dusanstojkovic/pengy/firmware/docs/CubeCell HTCC-AB01 - back.png

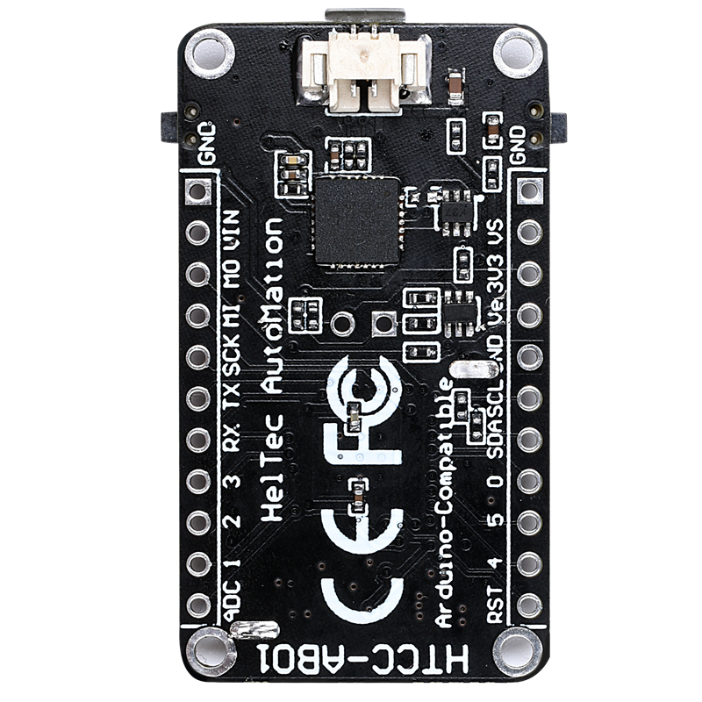
firmware/docs/CubeCell HTCC-AB01 - back.png
