dusanstojkovic/pengy/media/QI emojis/AQI emoji - Good.png

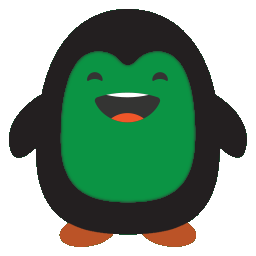
media/QI emojis/AQI emoji - Good.png
