dusanstojkovic/pengy/media/QI emojis/AQI emoji - Moderate.png

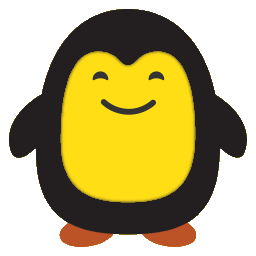
media/QI emojis/AQI emoji - Moderate.png
