dusanstojkovic/pengy/media/QI emojis/AQI emoji - Unhealthy.png

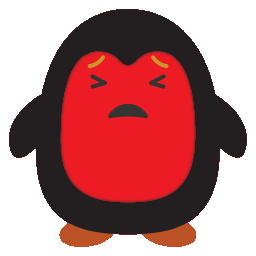
media/QI emojis/AQI emoji - Unhealthy.png
