dusanstojkovic/pengy/media/Construction Kit v1.0.jpg

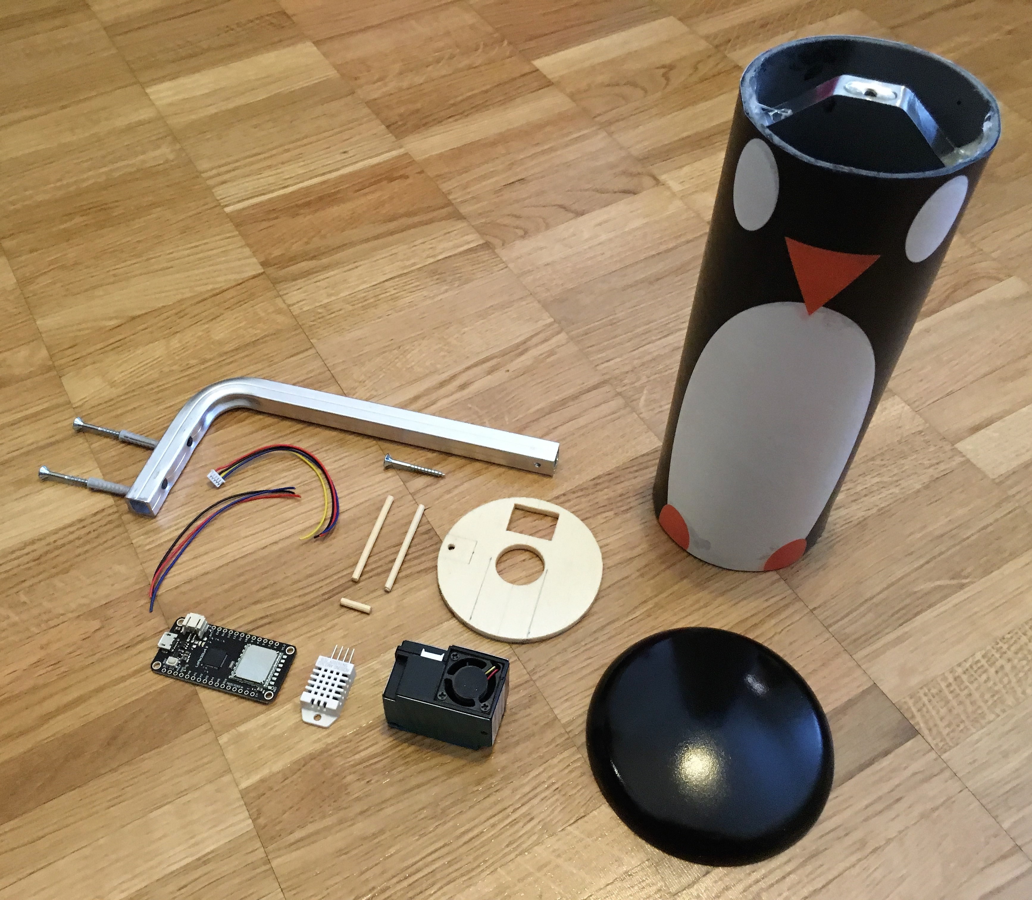
media/Construction Kit v1.0.jpg
